cdntinker/The-Nerd-Mage-Module-Programmer/Pix/blank (back).png

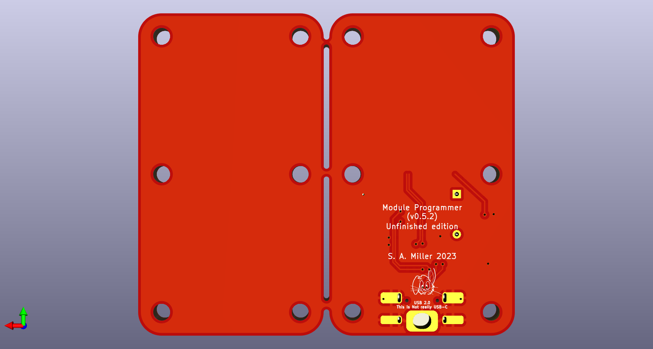
Pix/blank (back).png
