cdntinker/The-Nerd-Mage-Module-Programmer/Pix/Wio-RP2040 (back).png

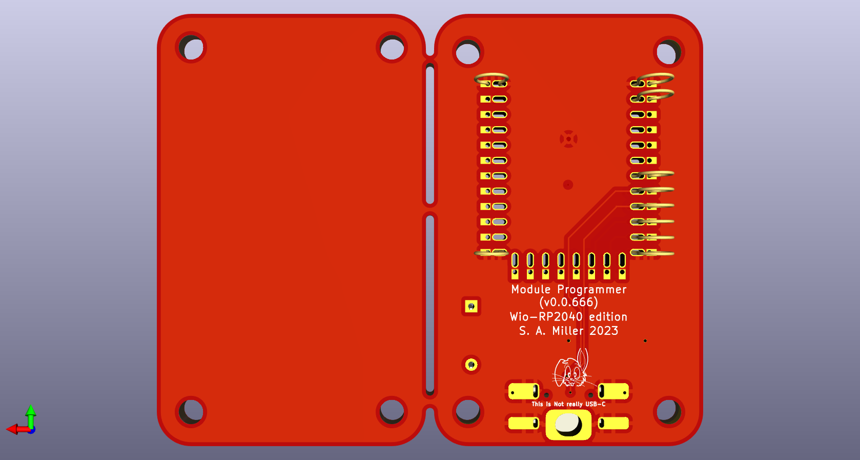
Pix/Wio-RP2040 (back).png
