cdntinker/The-Nerd-Mage-Module-Programmer/Pix/Wio-RP2040 (front).png

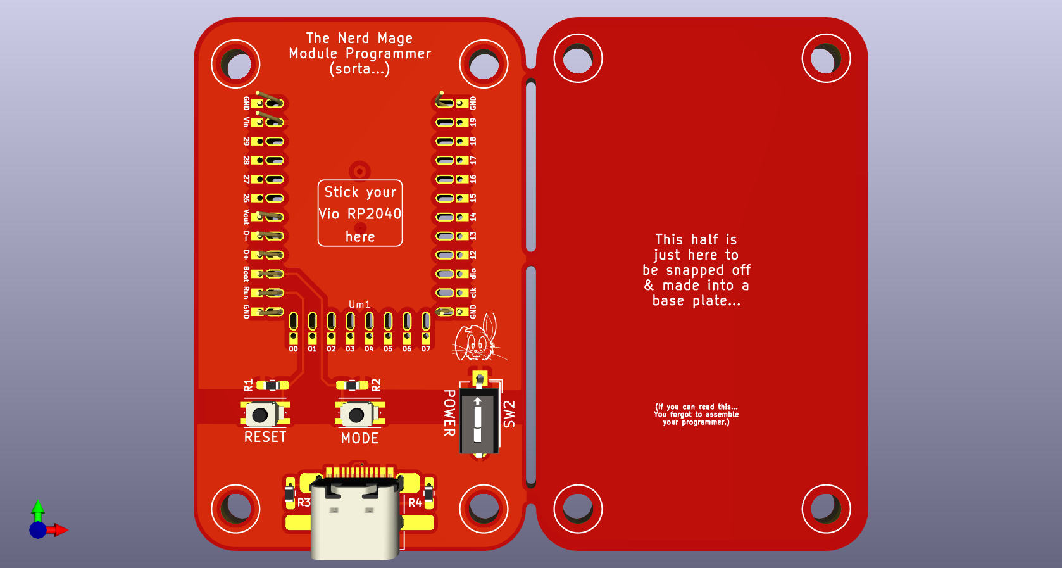
Pix/Wio-RP2040 (front).png
